vvyroubal/LabRax-components/usw-flex-mini/stl/tray_usw_l.stl

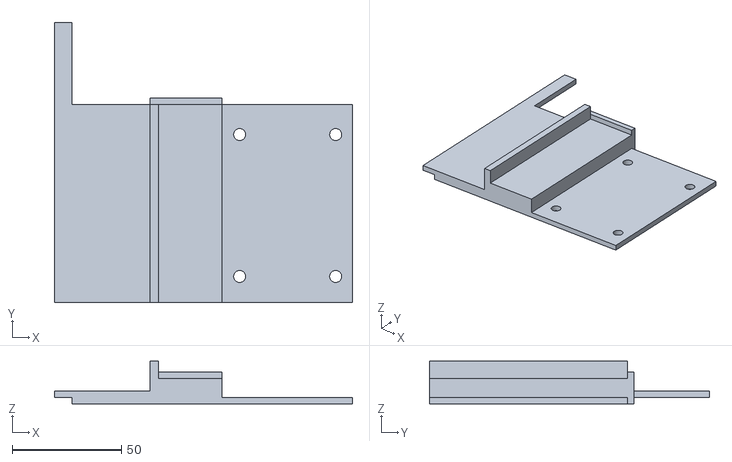
[picture p24: CAD file, 2026-10-03]
usw-flex-mini/stl/tray_usw_l.stl
136.5 x 128.4 x 19.6
