vvyroubal/LabRax-components/usw-flex-mini/USW_Flex_LabRax.step

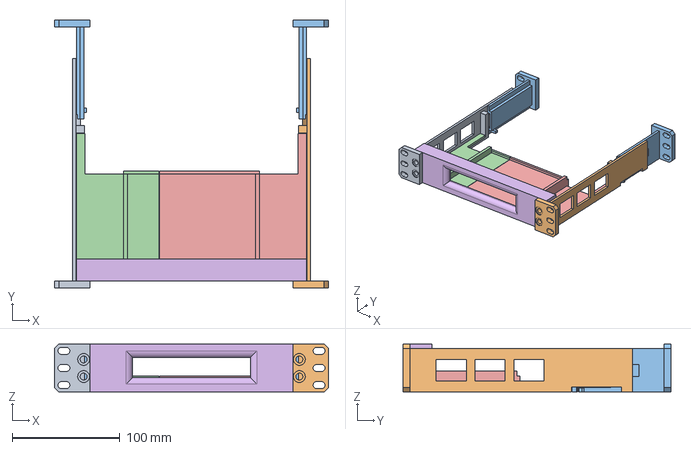
[picture p25: CAD file, 2026-10-03]
usw-flex-mini/USW_Flex_LabRax.step
254.0 x 248.0 x 44.5 mm
