vvyroubal/LabRax-components/common/stl/side_l.stl

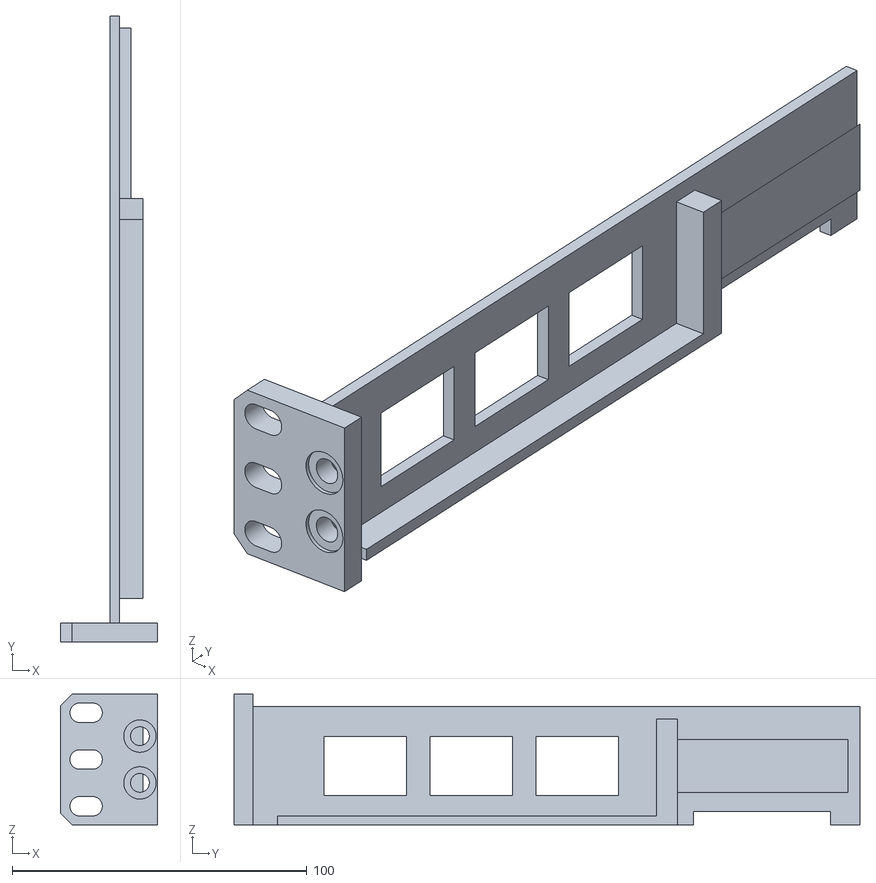
[picture p26: CAD file, 2026-10-03]
common/stl/side_l.stl
33.0 x 212.5 x 44.5
