vvyroubal/LabRax-components/nuc6i7kyk/stl/tray_nuc_r.stl

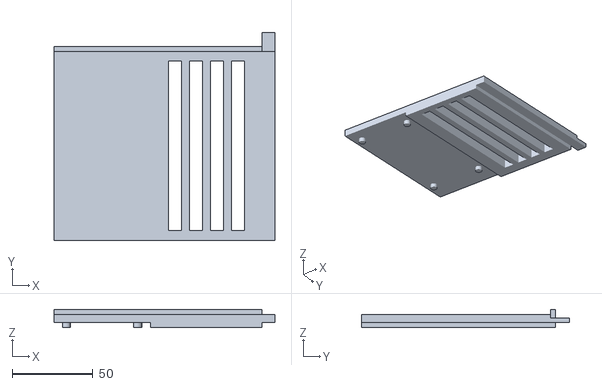
[picture p27: CAD file, 2026-10-03]
nuc6i7kyk/stl/tray_nuc_r.stl
136.5 x 128.4 x 11.2
