vvyroubal/LabRax-components/tl-sg108e/stl/tray_sg108e_l.stl

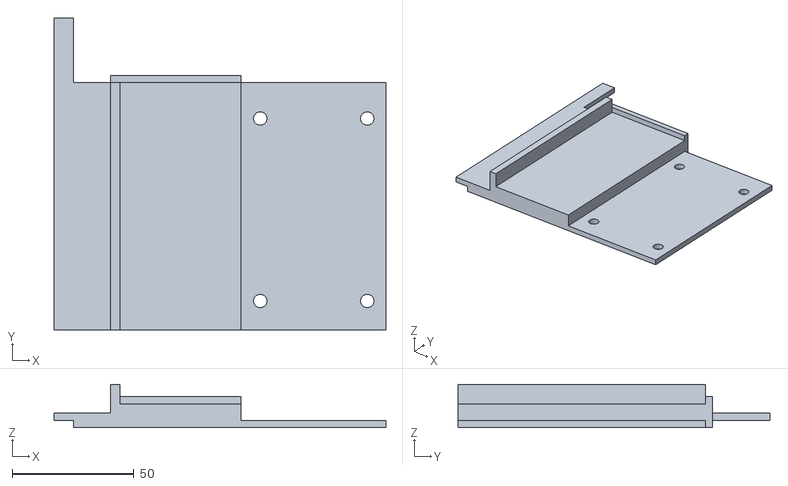
[picture p28: CAD file, 2026-10-03]
tl-sg108e/stl/tray_sg108e_l.stl
136.5 x 128.4 x 17.7
