vvyroubal/LabRax-components/ucg-fiber/stl/faceplate_ucg.stl

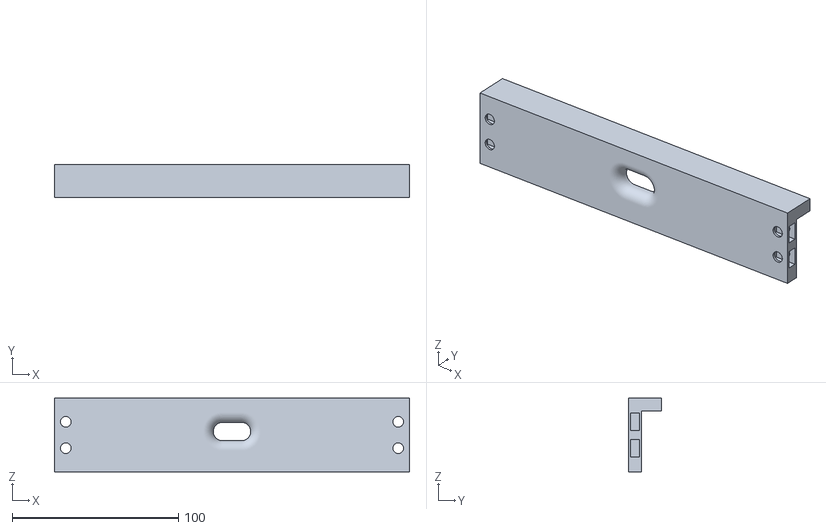
[picture p29: CAD file, 2026-10-03]
ucg-fiber/stl/faceplate_ucg.stl
213.6 x 20.0 x 44.5
