vvyroubal/LabRax-components/usw-flex-mini/stl/tray_usw_r.stl

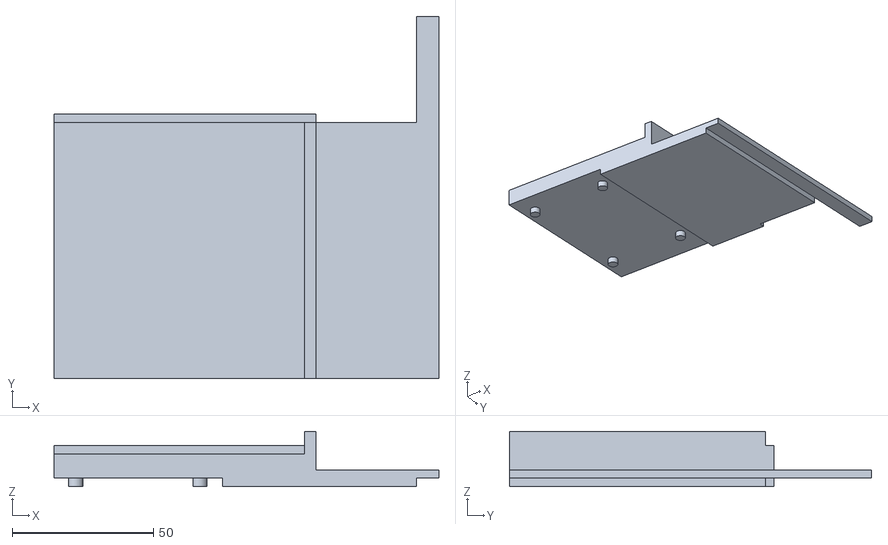
[picture p30: CAD file, 2026-10-03]
usw-flex-mini/stl/tray_usw_r.stl
136.5 x 128.4 x 19.6
