vvyroubal/LabRax-components/common/stl/coupon_tongue.stl

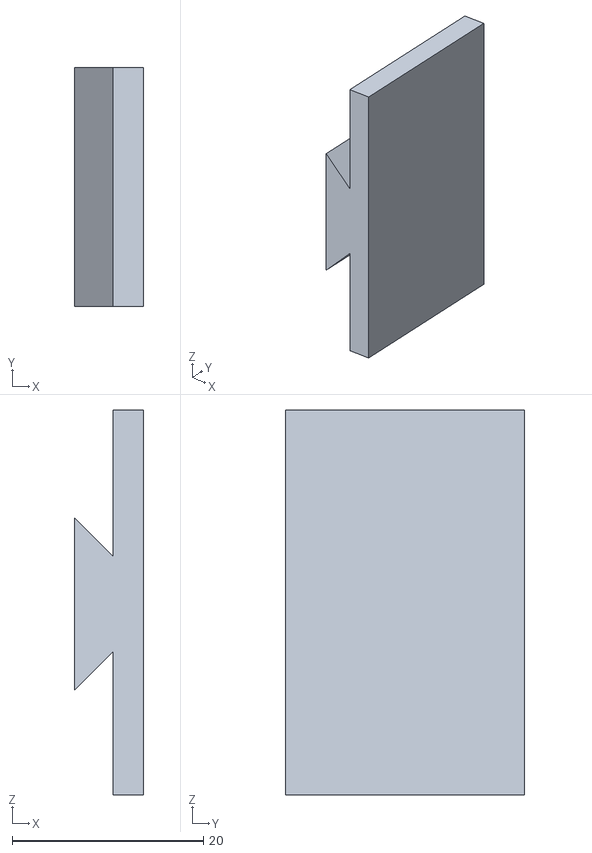
[picture p31: CAD file, 2026-10-03]
common/stl/coupon_tongue.stl
7.20 x 25.0 x 40.3
