vvyroubal/LabRax-components/nuc6i7kyk/images/assembly-nuc-top.png

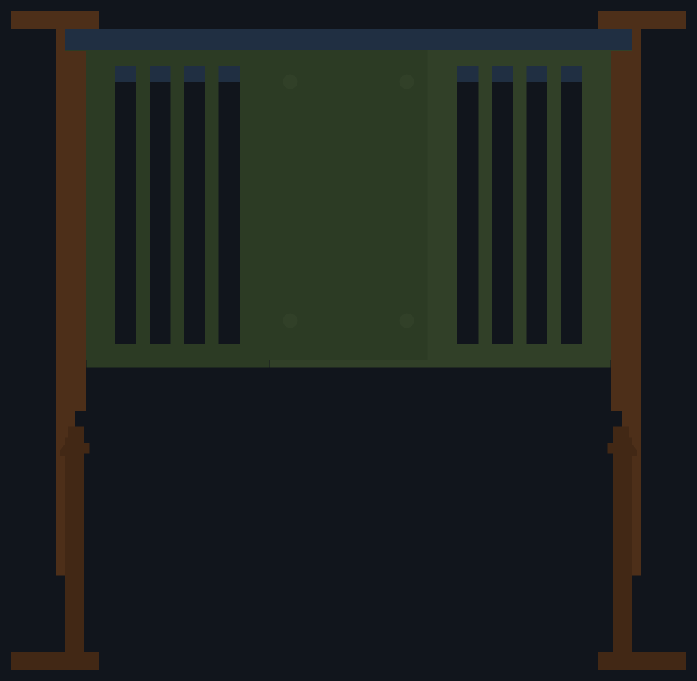
nuc6i7kyk/images/assembly-nuc-top.png
