vvyroubal/LabRax-components/nuc6i7kyk/images/makerworld-nuc-assembled.png

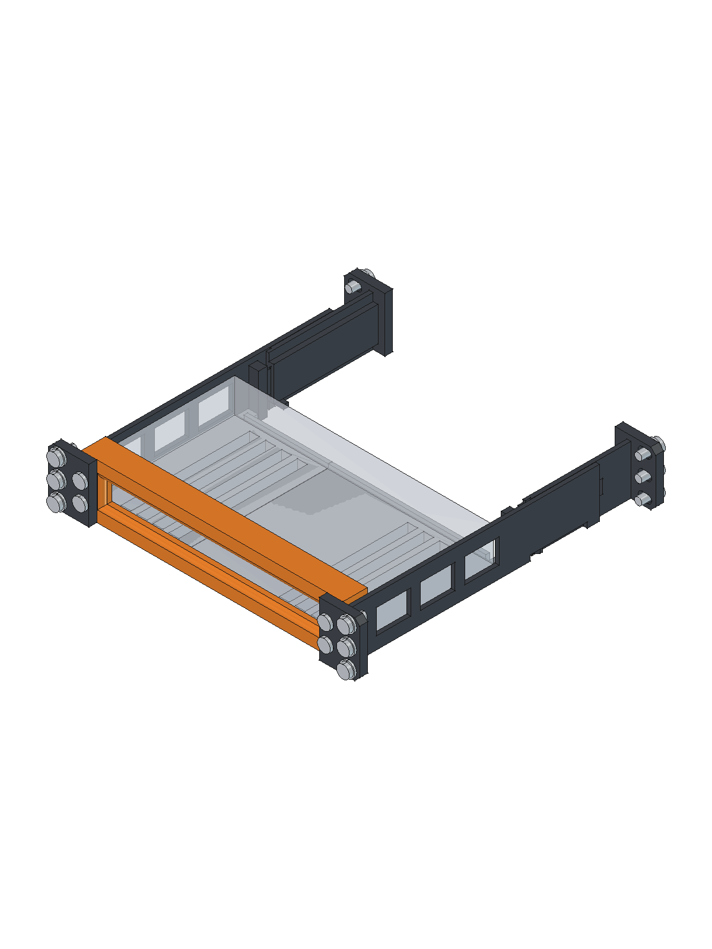
nuc6i7kyk/images/makerworld-nuc-assembled.png
