vvyroubal/LabRax-components/nuc6i7kyk/images/makerworld-nuc-exploded.png

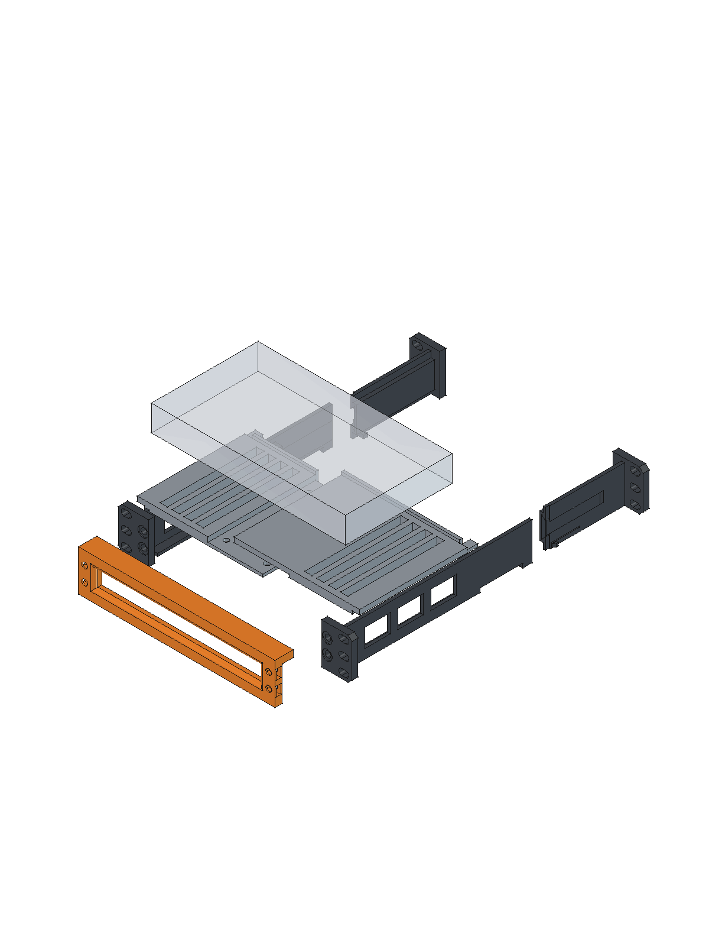
nuc6i7kyk/images/makerworld-nuc-exploded.png
